splitkb/halcyon/Case files/Ferris/Halcyon Ferris Sound Plate - 0.1mm Kerf.dxf

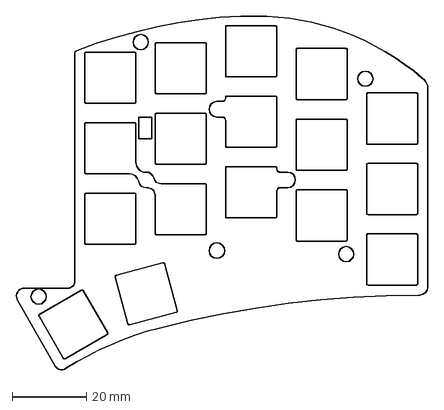
[picture p18: CAD file, 2025-07-31]
Case files/Ferris/Halcyon Ferris Sound Plate - 0.1mm Kerf.dxf
111.0 x 95.4 mm
