splitkb/halcyon/Case files/Kyria/Kyria rev4 Top Plate - No Puck - 0.1mm Kerf.dxf

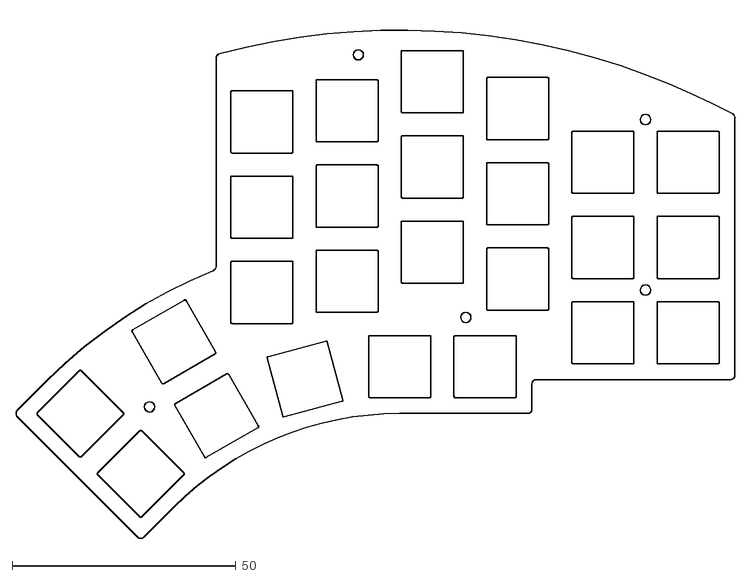
[picture p19: CAD file, 2024-09-05]
Case files/Kyria/Kyria rev4 Top Plate - No Puck - 0.1mm Kerf.dxf
160.7 x 116.8
