splitkb/halcyon/Case files/Elora/Elora rev2 Bottom Plate - No Kerf.dxf

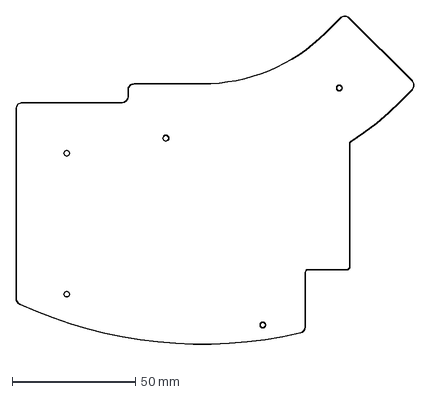
[picture p22: CAD file, 2025-01-30]
Case files/Elora/Elora rev2 Bottom Plate - No Kerf.dxf
161.3 x 137.3 mm
