splitkb/halcyon/Case files/Ferris/Halcyon Ferris Encoder OLED Cover - No Kerf.dxf

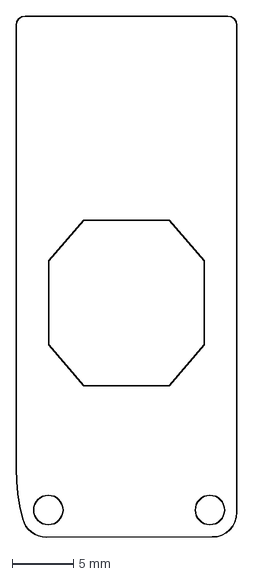
[picture p23: CAD file, 2025-07-31]
Case files/Ferris/Halcyon Ferris Encoder OLED Cover - No Kerf.dxf
18.0 x 42.5 mm
