splitkb/halcyon/Case files/Kyria/Kyria rev4 Bottom Plate - Puck - 0.1mm Kerf.dxf

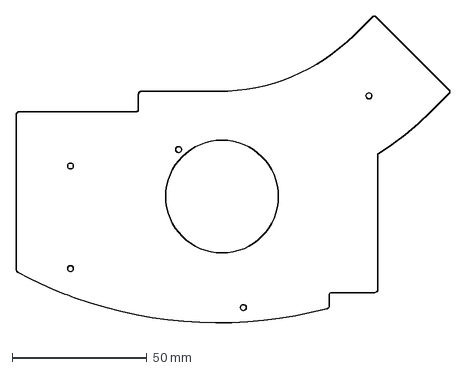
[picture p24: CAD file, 2024-09-05]
Case files/Kyria/Kyria rev4 Bottom Plate - Puck - 0.1mm Kerf.dxf
161.0 x 116.8 mm
