splitkb/halcyon/Case files/Lily58/Halcyon Lily58 Bottom Plate - No Kerf.dxf

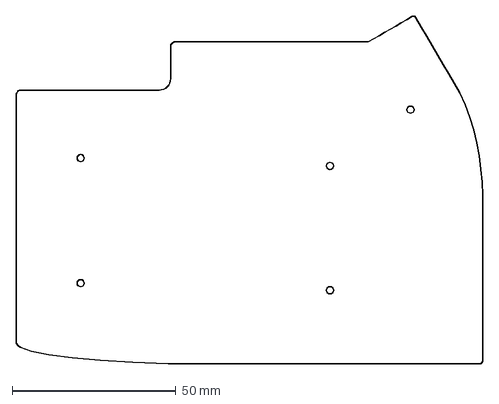
[picture p25: CAD file, 2025-07-31]
Case files/Lily58/Halcyon Lily58 Bottom Plate - No Kerf.dxf
142.5 x 106.3 mm
