splitkb/halcyon/Case files/Corne/Halcyon Corne Cirque Trackpad OLED Cover - No Kerf.dxf

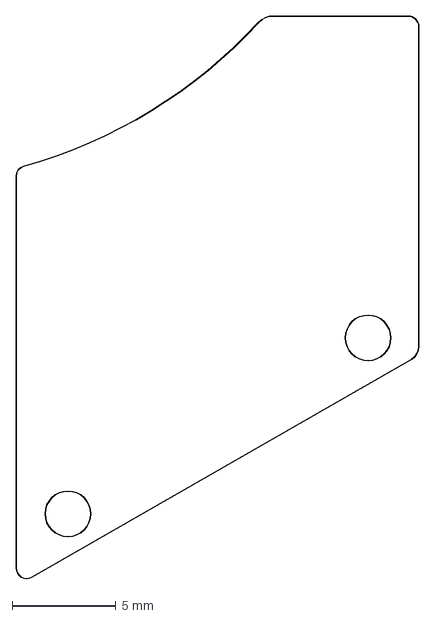
[picture p26: CAD file, 2025-07-31]
Case files/Corne/Halcyon Corne Cirque Trackpad OLED Cover - No Kerf.dxf
19.5 x 27.2 mm
