splitkb/halcyon/Case files/Kyria/Kyria rev4 Top Plate - No Puck - No Kerf.dxf

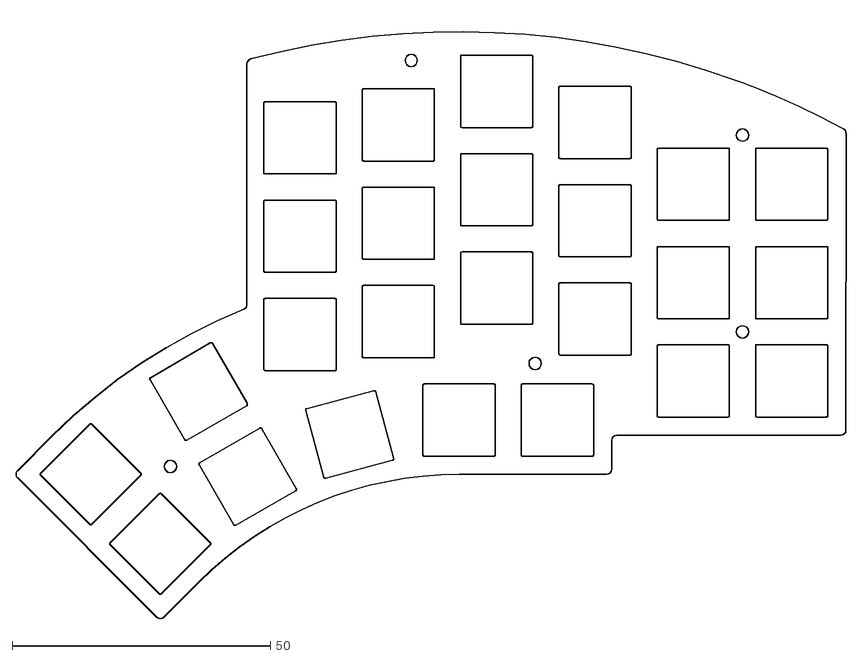
[picture p29: CAD file, 2024-09-05]
Case files/Kyria/Kyria rev4 Top Plate - No Puck - No Kerf.dxf
160.8 x 116.6
