splitkb/halcyon/Case files/Corne/Halcyon Corne Bottom Plate - Puck - No kerf.dxf

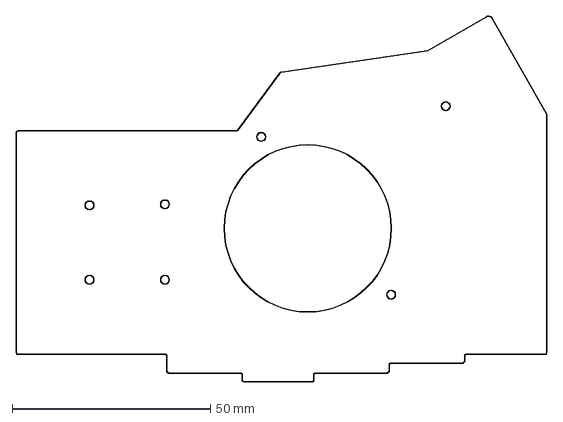
[picture p31: CAD file, 2025-07-31]
Case files/Corne/Halcyon Corne Bottom Plate - Puck - No kerf.dxf
133.8 x 92.2 mm
