splitkb/halcyon/Case files/Elora/Elora rev2 Bottom Plate - Puck - 0.1mm Kerf.dxf

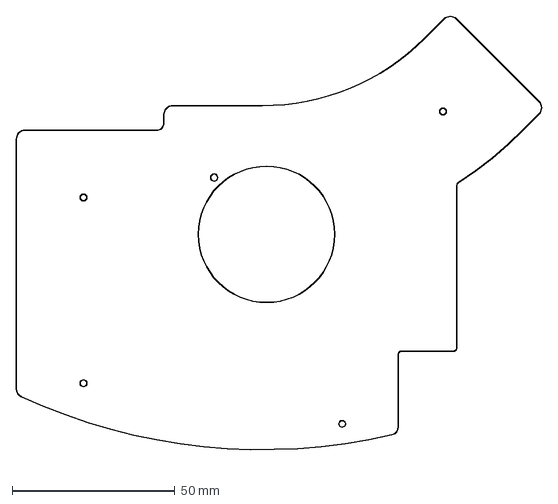
[picture p32: CAD file, 2025-01-30]
Case files/Elora/Elora rev2 Bottom Plate - Puck - 0.1mm Kerf.dxf
161.5 x 137.5 mm
