splitkb/halcyon/Case files/Kyria/Kyria rev4 Bottom Plate - Puck - No Kerf.dxf

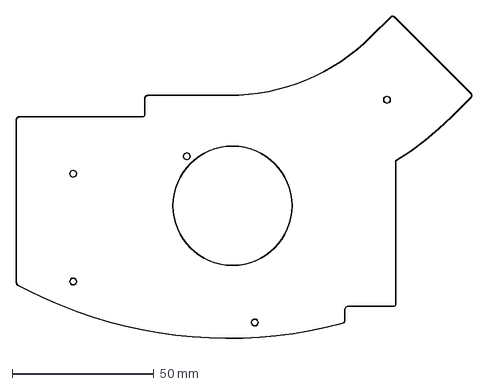
[picture p34: CAD file, 2024-09-05]
Case files/Kyria/Kyria rev4 Bottom Plate - Puck - No Kerf.dxf
160.8 x 116.6 mm
