splitkb/halcyon/Case files/Lily58/Halcyon Lily58 Cirque OLED Cover - 0.1mm Kerf.dxf

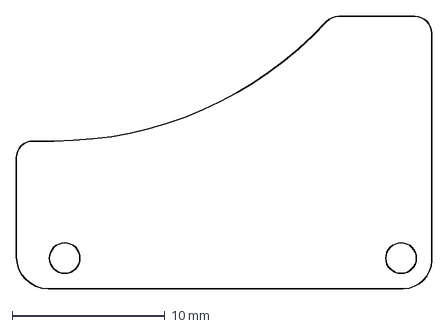
[picture p35: CAD file, 2025-07-31]
Case files/Lily58/Halcyon Lily58 Cirque OLED Cover - 0.1mm Kerf.dxf
27.2 x 17.8 mm
