splitkb/halcyon/Case files/Corne/Halcyon Corne Sound Plate - 0.1mm Kerf.dxf

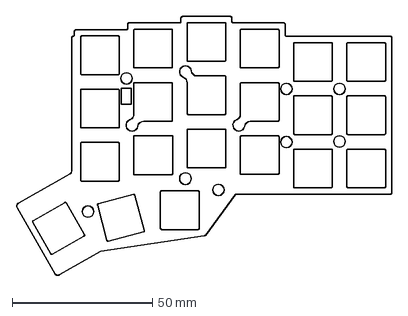
[picture p36: CAD file, 2025-07-31]
Case files/Corne/Halcyon Corne Sound Plate - 0.1mm Kerf.dxf
133.9 x 92.4 mm
