splitkb/halcyon/Case files/Kyria/Kyria rev4 Top Plate - 0.1mm Kerf.dxf

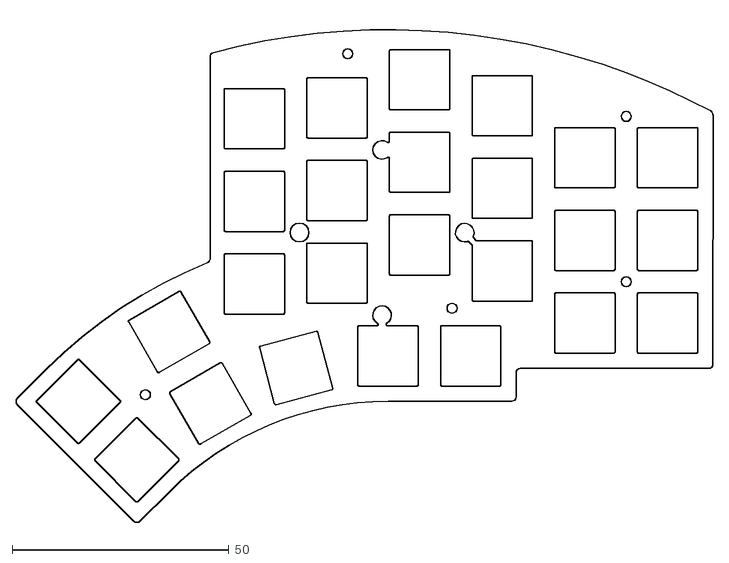
[picture p39: CAD file, 2024-09-05]
Case files/Kyria/Kyria rev4 Top Plate - 0.1mm Kerf.dxf
160.7 x 116.8
