splitkb/halcyon/Case files/Corne/Halcyon Corne Top Plate - 0.1mm kerf.dxf

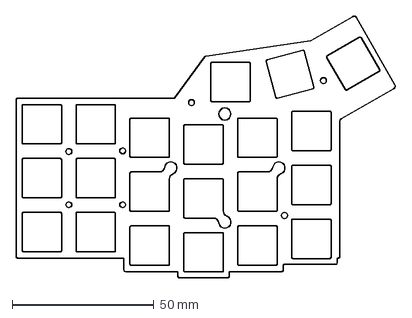
[picture p41: CAD file, 2025-07-31]
Case files/Corne/Halcyon Corne Top Plate - 0.1mm kerf.dxf
133.8 x 92.3 mm
