splitkb/halcyon/Case files/Ferris/Halcyon Ferris Short OLED Cover - 0.1mm Kerf.dxf

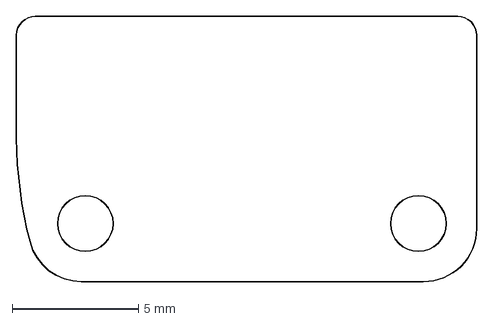
[picture p43: CAD file, 2025-07-31]
Case files/Ferris/Halcyon Ferris Short OLED Cover - 0.1mm Kerf.dxf
18.2 x 10.5 mm
