splitkb/halcyon/Case files/Corne/Halcyon Corne Bottom Plate - Puck - 0.1mm Kerf.dxf

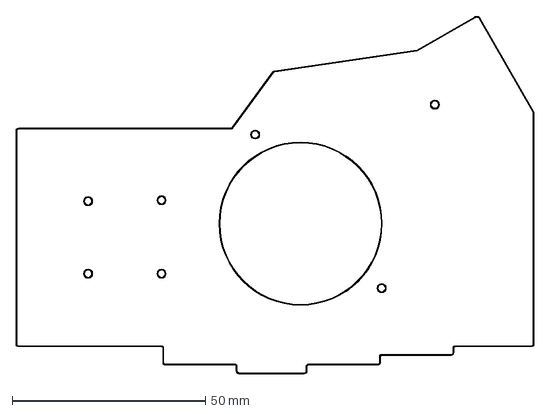
[picture p46: CAD file, 2025-07-31]
Case files/Corne/Halcyon Corne Bottom Plate - Puck - 0.1mm Kerf.dxf
134.0 x 92.4 mm
