splitkb/halcyon/Case files/Elora/Elora rev2 OLED Cover - No Kerf.dxf

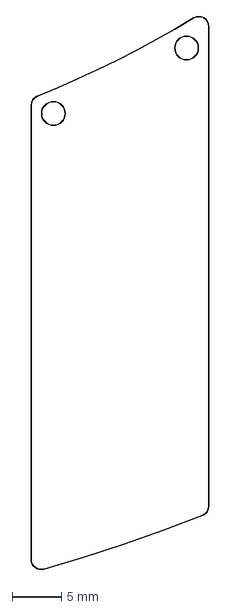
[picture p47: CAD file, 2024-09-05]
Case files/Elora/Elora rev2 OLED Cover - No Kerf.dxf
18.0 x 56.1 mm
