splitkb/halcyon/Case files/Corne/Halcyon Corne Short OLED Cover - 0.1mm Kerf.dxf

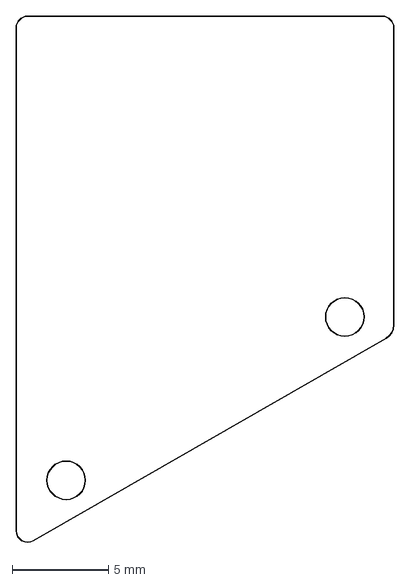
[picture p50: CAD file, 2025-07-31]
Case files/Corne/Halcyon Corne Short OLED Cover - 0.1mm Kerf.dxf
19.7 x 27.4 mm
