splitkb/halcyon/Case files/Elora/Elora rev2 Short OLED Cover - 0.1mm Kerf.dxf

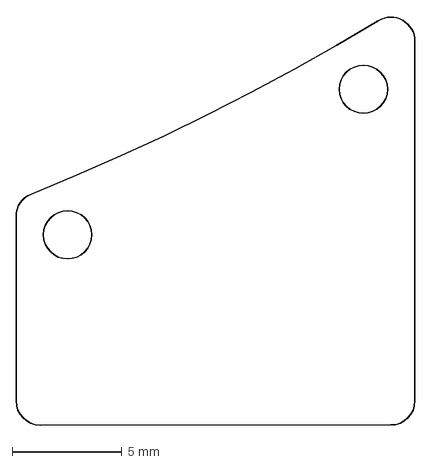
[picture p51: CAD file, 2024-09-05]
Case files/Elora/Elora rev2 Short OLED Cover - 0.1mm Kerf.dxf
18.2 x 18.7 mm
