splitkb/halcyon/Case files/Ferris/Halcyon Ferris Sound Plate - No Kerf.dxf

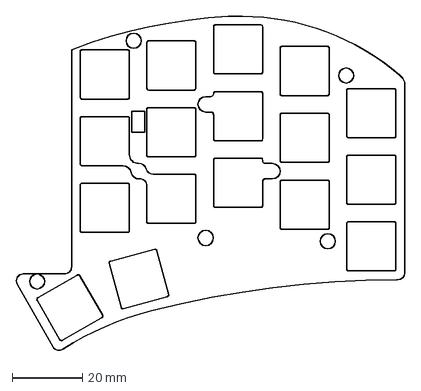
[picture p52: CAD file, 2025-07-31]
Case files/Ferris/Halcyon Ferris Sound Plate - No Kerf.dxf
110.8 x 95.2 mm
