splitkb/halcyon/Case files/Corne/Halcyon Corne Encoder OLED Cover - 0.1mm Kerf.dxf

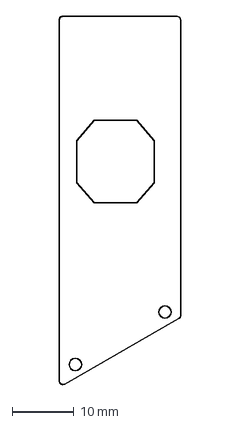
[picture p54: CAD file, 2025-07-31]
Case files/Corne/Halcyon Corne Encoder OLED Cover - 0.1mm Kerf.dxf
19.7 x 59.6 mm
