splitkb/halcyon/Case files/Elora/Elora rev2 Cirque Trackpad OLED Cover - No Kerf.dxf

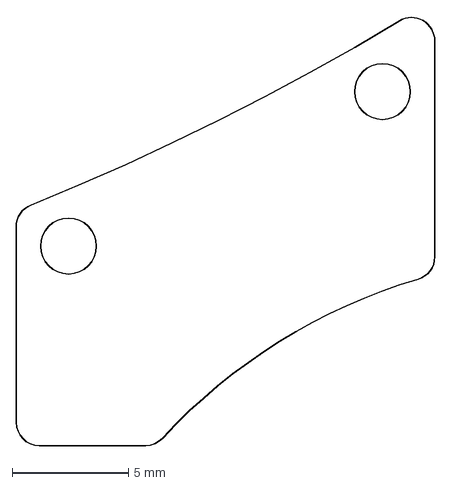
[picture p55: CAD file, 2024-09-05]
Case files/Elora/Elora rev2 Cirque Trackpad OLED Cover - No Kerf.dxf
18.0 x 18.5 mm
