splitkb/halcyon/Case files/Ferris/Halcyon Ferris Bottom Plate - Puck - 0.1mm Kerf.dxf

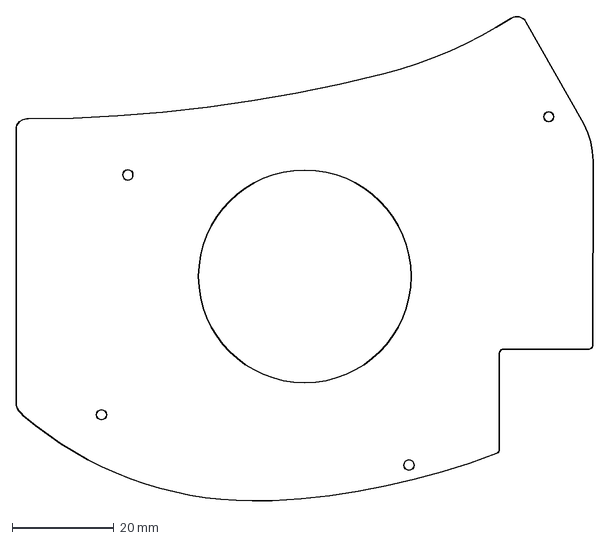
[picture p56: CAD file, 2025-07-31]
Case files/Ferris/Halcyon Ferris Bottom Plate - Puck - 0.1mm Kerf.dxf
113.7 x 95.4 mm
