splitkb/halcyon/Case files/Corne/Halcyon Corne Bottom Plate - 0.1mm kerf.dxf

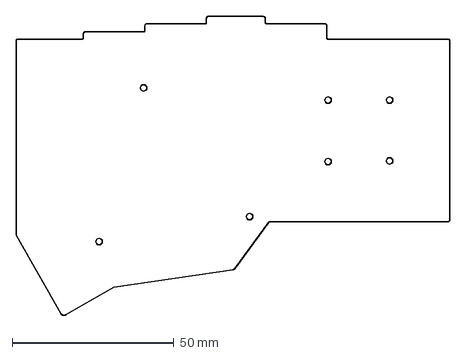
[picture p58: CAD file, 2025-07-31]
Case files/Corne/Halcyon Corne Bottom Plate - 0.1mm kerf.dxf
134.0 x 92.4 mm
