splitkb/halcyon/Case files/Elora/Elora rev2 Cirque Trackpad OLED Cover - 0.1mm Kerf.dxf

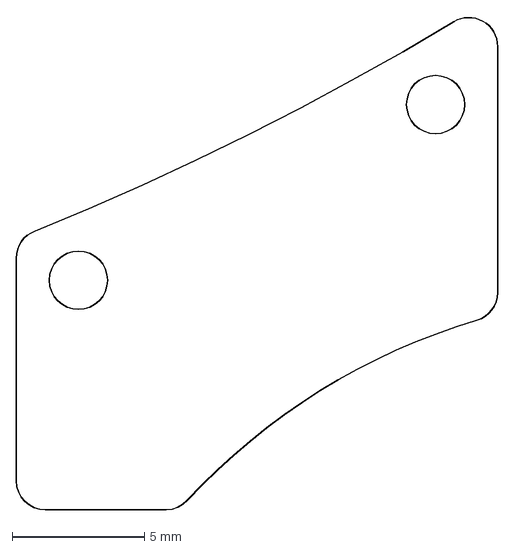
[picture p59: CAD file, 2024-09-05]
Case files/Elora/Elora rev2 Cirque Trackpad OLED Cover - 0.1mm Kerf.dxf
18.2 x 18.7 mm
