splitkb/halcyon/Case files/Ferris/Halcyon Ferris Top Plate - No Kerf.dxf

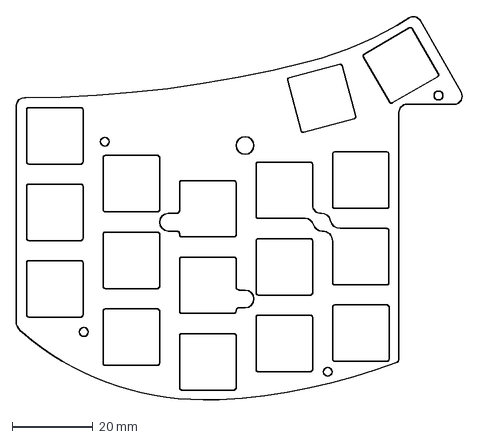
[picture p60: CAD file, 2025-07-31]
Case files/Ferris/Halcyon Ferris Top Plate - No Kerf.dxf
110.8 x 95.2 mm
