splitkb/halcyon/Case files/Corne/Halcyon Corne OLED Cover - 0.1mm Kerf.dxf

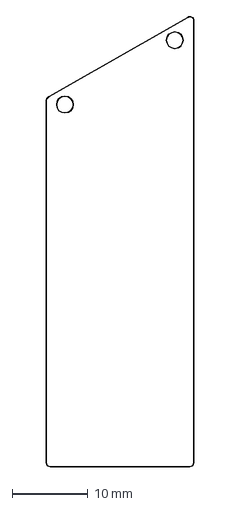
[picture p62: CAD file, 2025-07-31]
Case files/Corne/Halcyon Corne OLED Cover - 0.1mm Kerf.dxf
19.5 x 59.4 mm
