splitkb/halcyon/Case files/Elora/Elora rev2 Short OLED Cover - No Kerf.dxf

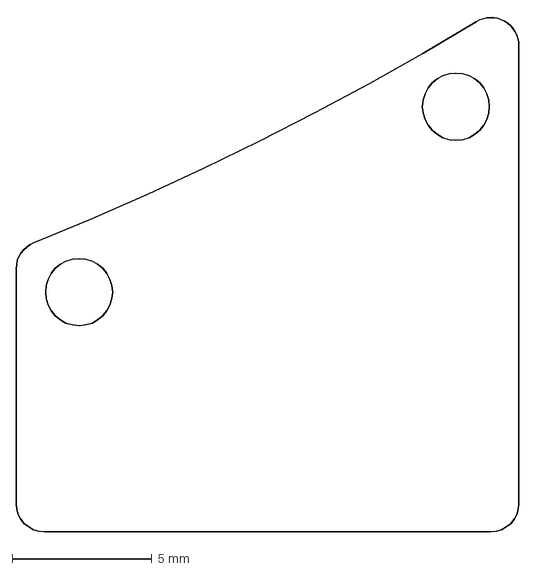
[picture p63: CAD file, 2024-09-05]
Case files/Elora/Elora rev2 Short OLED Cover - No Kerf.dxf
18.0 x 18.5 mm
