splitkb/halcyon/Case files/Ferris/Halcyon Ferris Bottom Plate - No Kerf.dxf

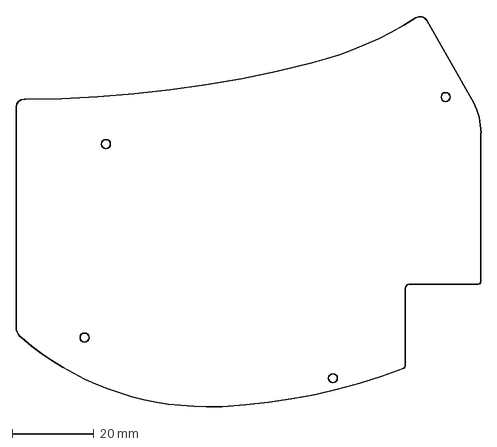
[picture p64: CAD file, 2025-07-31]
Case files/Ferris/Halcyon Ferris Bottom Plate - No Kerf.dxf
113.5 x 95.2 mm
