splitkb/halcyon/Case files/Lily58/Halcyon Lily58 OLED Cover - 0.1mm Kerf.dxf

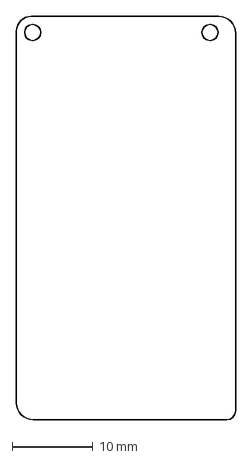
[picture p65: CAD file, 2025-07-31]
Case files/Lily58/Halcyon Lily58 OLED Cover - 0.1mm Kerf.dxf
27.2 x 50.0 mm
