splitkb/halcyon/Case files/Ferris/Halcyon Ferris Cirque OLED Cover - 0.1mm Kerf.dxf

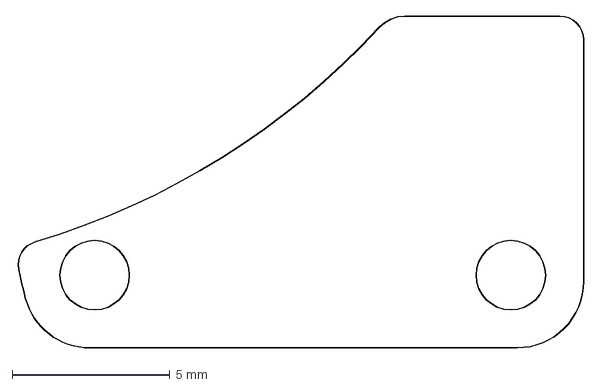
[picture p68: CAD file, 2025-07-31]
Case files/Ferris/Halcyon Ferris Cirque OLED Cover - 0.1mm Kerf.dxf
18.0 x 10.5 mm
