splitkb/halcyon/Case files/Elora/Elora rev2 Encoder OLED Cover - 0.1mm Kerf.dxf

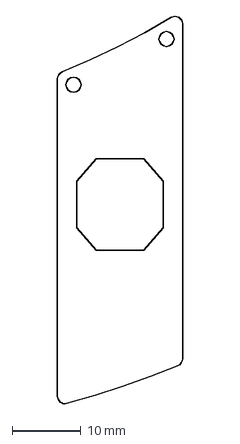
[picture p70: CAD file, 2024-09-05]
Case files/Elora/Elora rev2 Encoder OLED Cover - 0.1mm Kerf.dxf
18.2 x 56.3 mm
