splitkb/halcyon/Case files/Ferris/Halcyon Ferris Cirque OLED Cover - No Kerf.dxf

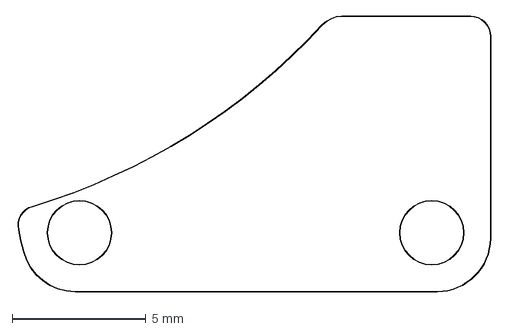
[picture p71: CAD file, 2025-07-31]
Case files/Ferris/Halcyon Ferris Cirque OLED Cover - No Kerf.dxf
17.7 x 10.3 mm
