splitkb/halcyon/Case files/Corne/Halcyon Corne Sound Plate - No Kerf.dxf

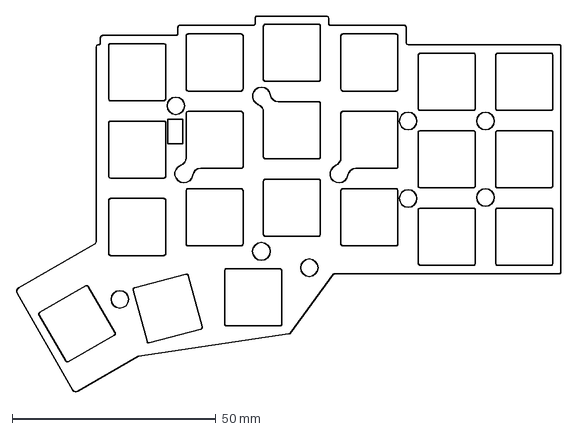
[picture p73: CAD file, 2025-07-31]
Case files/Corne/Halcyon Corne Sound Plate - No Kerf.dxf
133.7 x 92.2 mm
