splitkb/halcyon/Case files/Ferris/Halcyon Ferris OLED Cover - 0.1mm Kerf.dxf

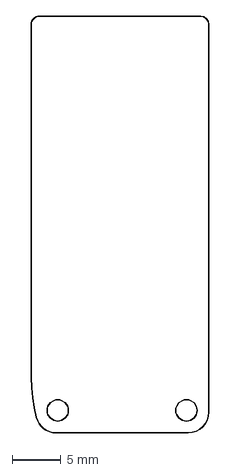
[picture p74: CAD file, 2025-07-31]
Case files/Ferris/Halcyon Ferris OLED Cover - 0.1mm Kerf.dxf
18.2 x 42.7 mm
