splitkb/halcyon/Case files/Lily58/Halcyon Lily58 Encoder OLED Cover - No Kerf.dxf

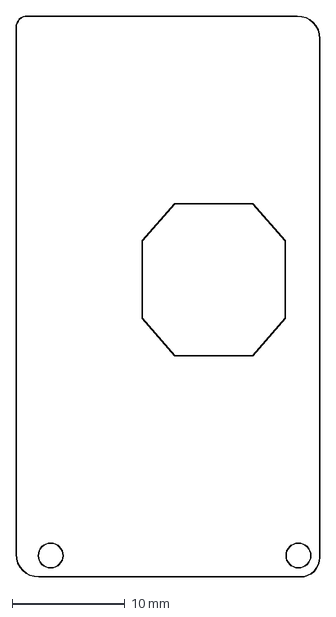
[picture p75: CAD file, 2025-07-31]
Case files/Lily58/Halcyon Lily58 Encoder OLED Cover - No Kerf.dxf
27.0 x 49.8 mm
