splitkb/halcyon/Case files/Lily58/Halcyon Lily58 Short OLED Cover - 0.1mm Kerf.dxf

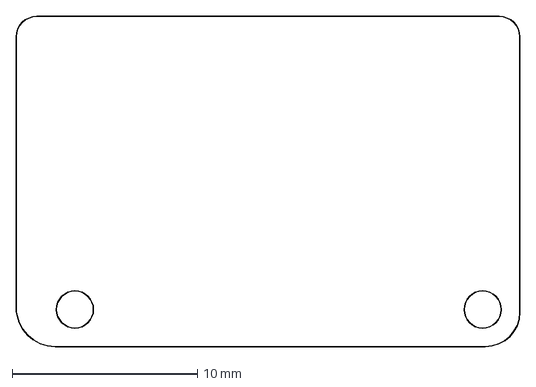
[picture p76: CAD file, 2025-07-31]
Case files/Lily58/Halcyon Lily58 Short OLED Cover - 0.1mm Kerf.dxf
27.2 x 17.8 mm
