splitkb/halcyon/Case files/Lily58/Halcyon Lily58 Sound Plate - 0.1mm Kerf.dxf

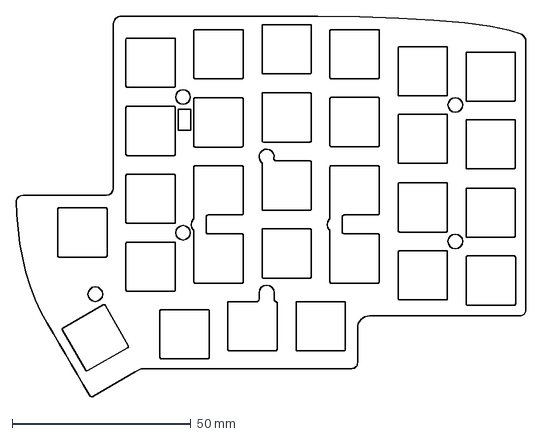
[picture p77: CAD file, 2025-07-31]
Case files/Lily58/Halcyon Lily58 Sound Plate - 0.1mm Kerf.dxf
142.7 x 106.5 mm
