splitkb/halcyon/Case files/Lily58/Halcyon Lily58 Cirque OLED Cover - No Kerf.dxf

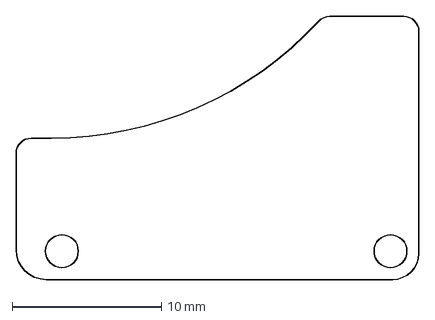
[picture p79: CAD file, 2025-07-31]
Case files/Lily58/Halcyon Lily58 Cirque OLED Cover - No Kerf.dxf
27.0 x 17.6 mm
