splitkb/halcyon/Halcyon Module Template/template-module/template-module.kicad_sch

## KiCad design Halcyon Module Template/template-module/template-module.kicad_sch (2024-09-11)

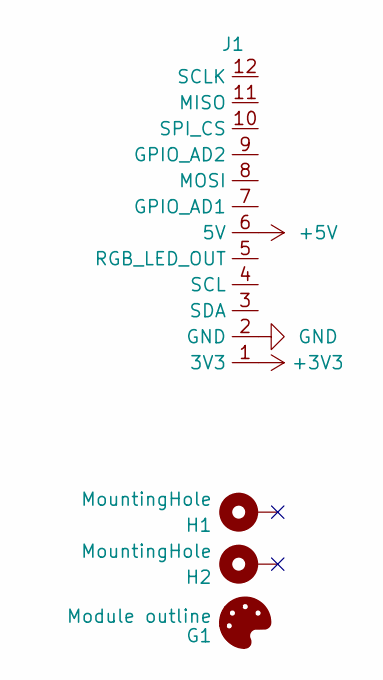
[picture p80: schematic template-module.kicad_sch]

Parts:
G1: Module outline; Module
H1, H2: MountingHole; Mounting_Wuerth_WA-SMSI-M1.6_H6mm_ThreadDepth2mm_97730606332
J1: vik-module-connector

Connections:
+3V3: J1.1 (3V3)
+5V: J1.6 (5V)
GND: J1.2 (GND)
